giangvo200837/Kwel---Spotwelder-Supercapacitor/Pictures/IMG_2326.jpg

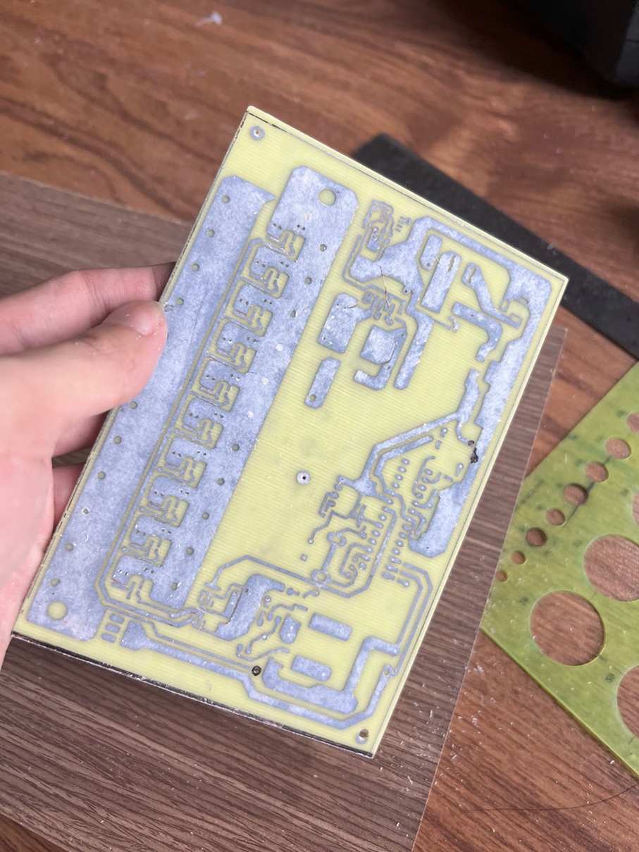
Pictures/IMG_2326.jpg
