giangvo200837/Kwel---Spotwelder-Supercapacitor/Pictures/IMG_2431.jpg

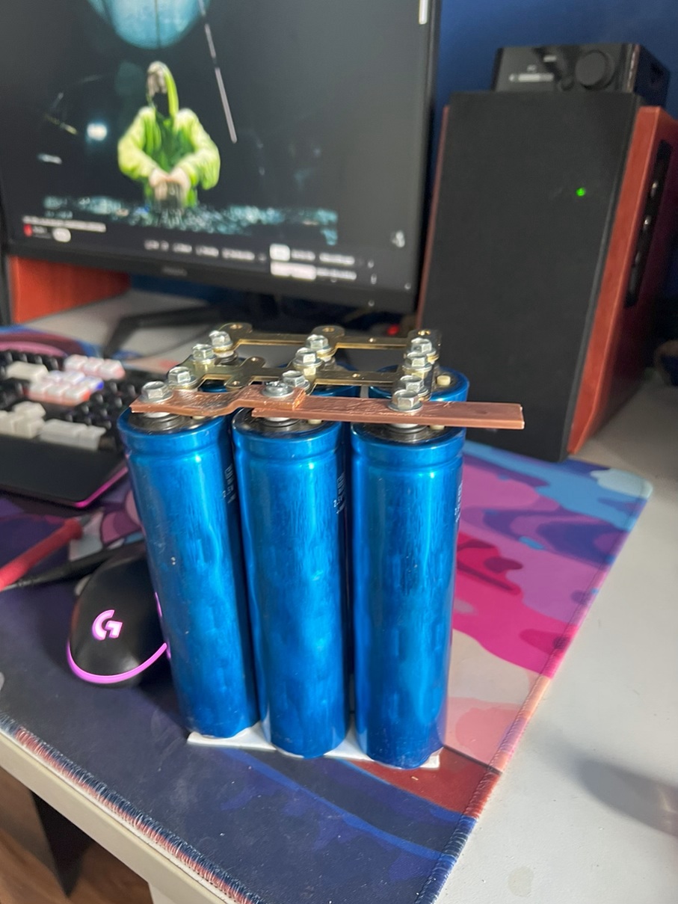
Pictures/IMG_2431.jpg
