giangvo200837/Kwel---Spotwelder-Supercapacitor/Pictures/IMG_2432.png

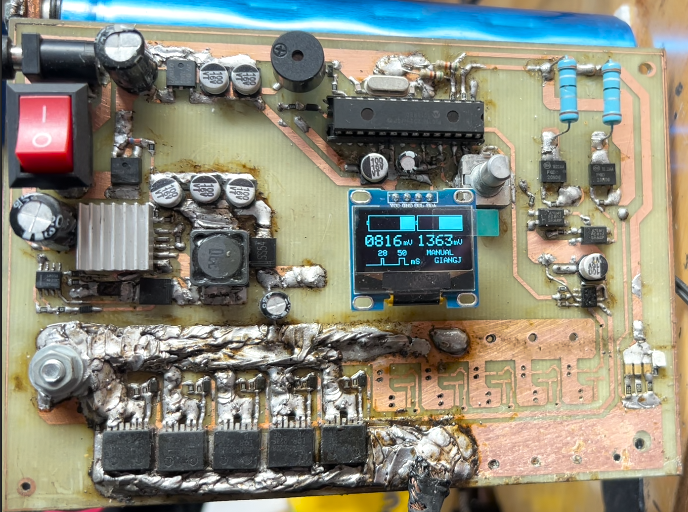
Pictures/IMG_2432.png
